DMGamage/Ventilator_Project/img/img2.png

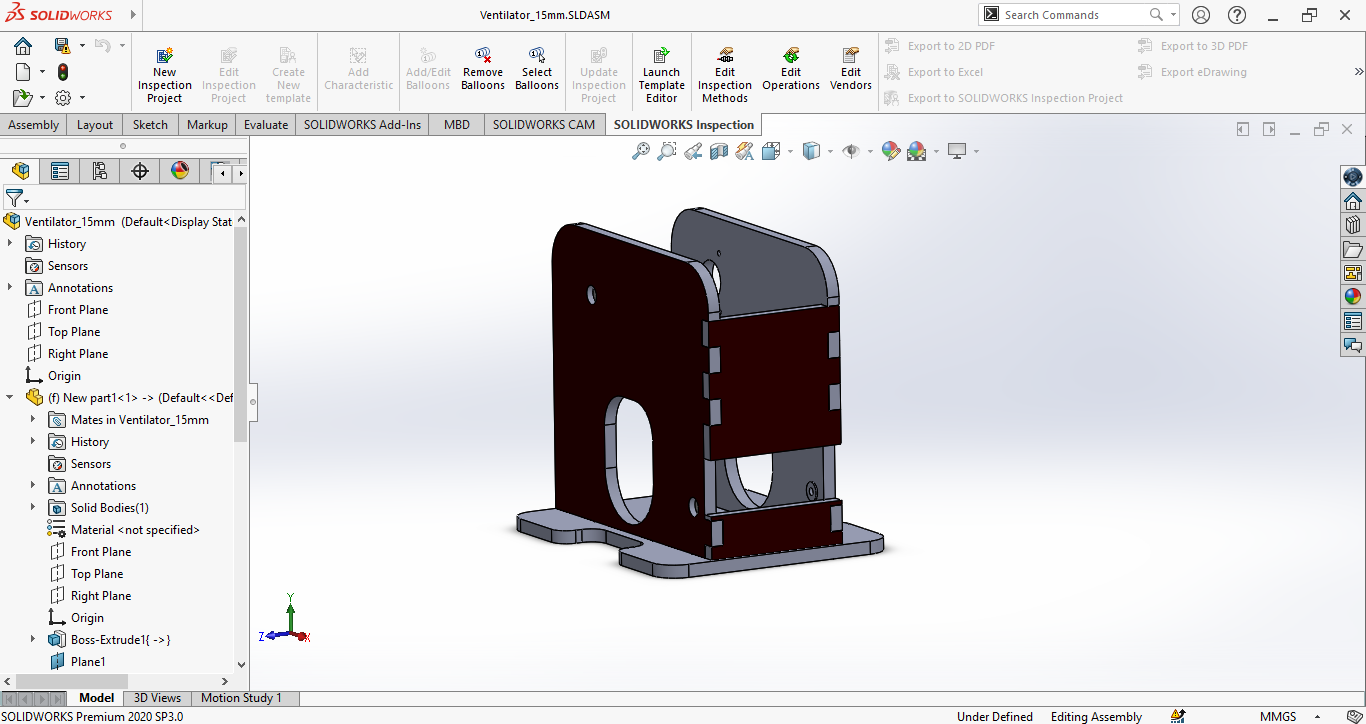
img/img2.png
