DMGamage/Ventilator_Project/img/img3.png

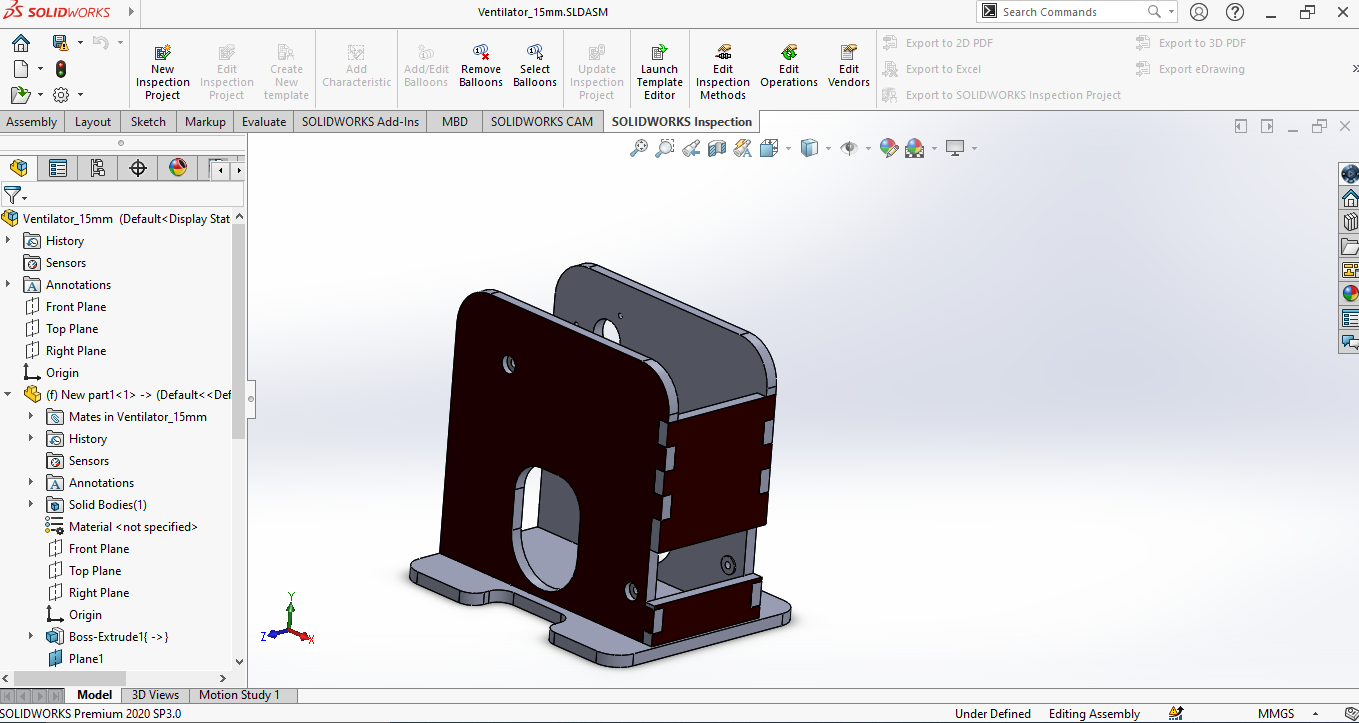
img/img3.png
