DMGamage/Ventilator_Project/Solidworks Files/New part2.SLDPRT

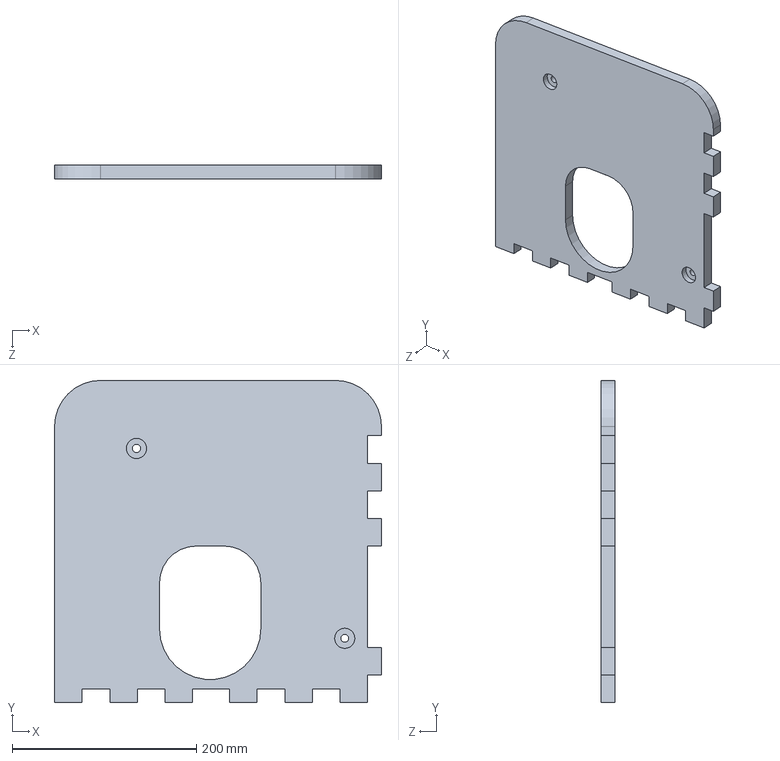
[picture p30: CAD file, 2022-12-30]
Solidworks Files/New part2.SLDPRT
355.0 x 349.8 x 15.0 mm
