DMGamage/Ventilator_Project/Solidworks Files/New part4.SLDPRT

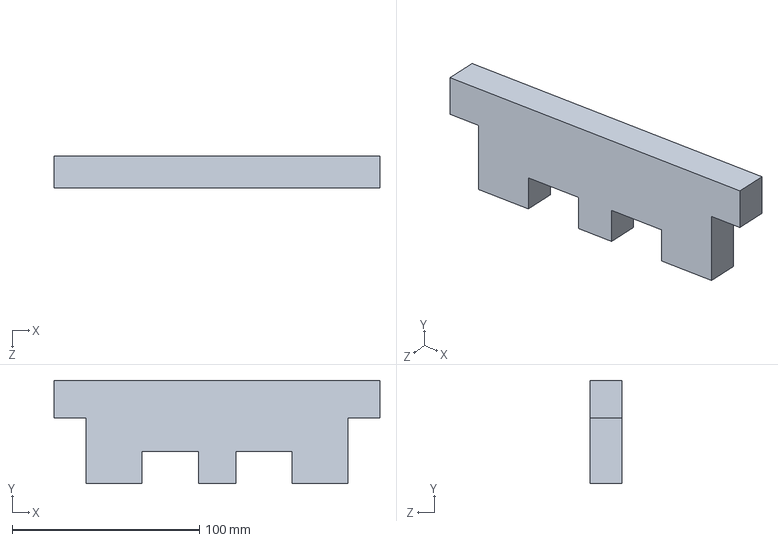
[picture p31: CAD file, 2022-12-30]
Solidworks Files/New part4.SLDPRT
174.0 x 55.0 x 17.0 mm
