DMGamage/Ventilator_Project/Solidworks Files/Thread.SLDPRT

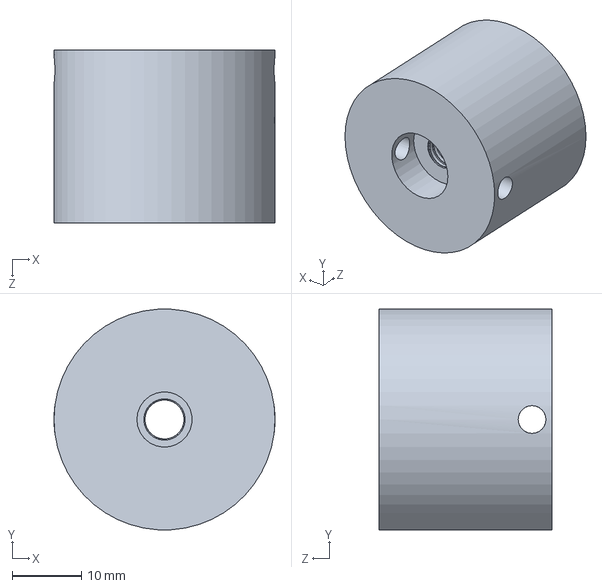
[picture p32: CAD file, 2022-12-30]
Solidworks Files/Thread.SLDPRT
32.0 x 31.9 x 25.0 mm
