DMGamage/Ventilator_Project/Solidworks Files/Part41.SLDPRT

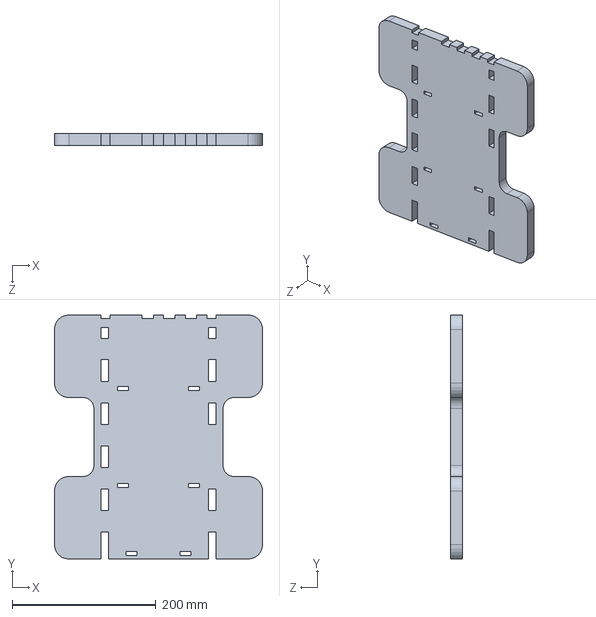
[picture p33: CAD file, 2022-12-30]
Solidworks Files/Part41.SLDPRT
290.0 x 340.0 x 17.0 mm
