DMGamage/Ventilator_Project/Solidworks Files/New part3.SLDPRT

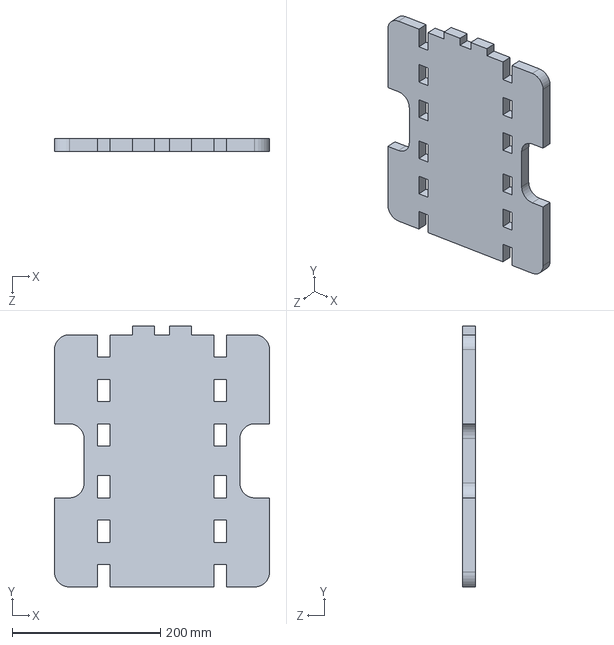
[picture p34: CAD file, 2022-12-30]
Solidworks Files/New part3.SLDPRT
290.0 x 351.8 x 17.0 mm
