DMGamage/Ventilator_Project/Solidworks Files/New part1.SLDPRT

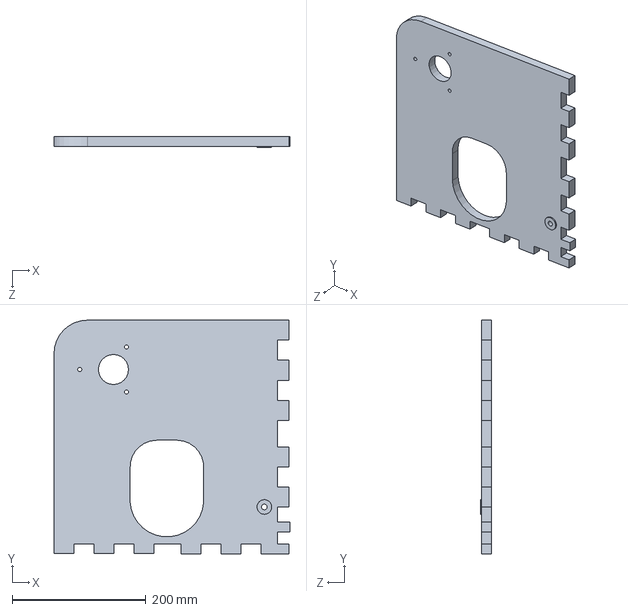
[picture p35: CAD file, 2022-12-30]
Solidworks Files/New part1.SLDPRT
353.4 x 349.9 x 17.0 mm
