DMGamage/Ventilator_Project/Solidworks Files/Front_Top.SLDPRT

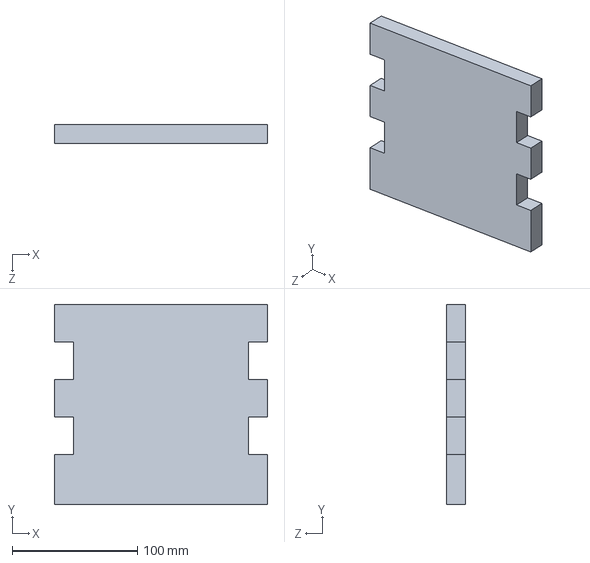
[picture p36: CAD file, 2022-12-30]
Solidworks Files/Front_Top.SLDPRT
170.0 x 160.0 x 15.0 mm
